unkyulee/macropad/images/005.jpeg

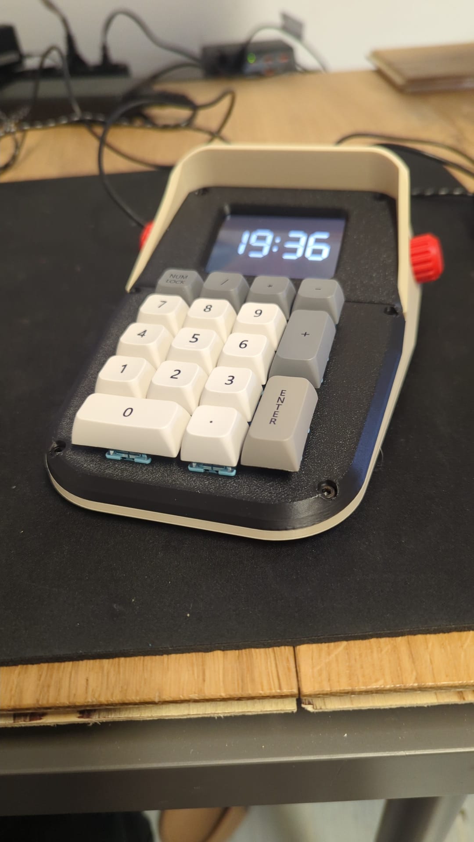
images/005.jpeg
