unkyulee/macropad/src/data/gif/youtube.gif

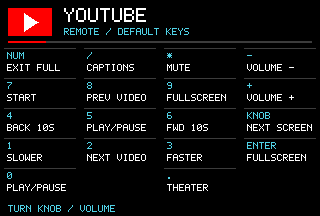
src/data/gif/youtube.gif
